raspyweather/githubHW/githubHW.cir

* C:\Users\Armin Beck\Documents\hw\githubHW.cir

* EESchema Netlist Version 1.1 (Spice format) creation date: 22.12.2017 06:53:42

* To exclude a component from the Spice Netlist add [Spice_Netlist_Enabled] user FIELD set to: N
* To reorder the component spice node sequence add [Spice_Node_Sequence] user FIELD and define sequence: 2,1,0

* Sheet Name: /
D65  Net-_D100-Pad1_ Net-_D50-Pad2_ LED		
D64  Net-_D106-Pad1_ Net-_D50-Pad2_ LED		
D66  Net-_D101-Pad1_ Net-_D50-Pad2_ LED		
D67  Net-_D102-Pad1_ Net-_D50-Pad2_ LED		
D68  Net-_D103-Pad1_ Net-_D50-Pad2_ LED		
D69  Net-_D104-Pad1_ Net-_D50-Pad2_ LED		
D70  Net-_D105-Pad1_ Net-_D50-Pad2_ LED		
D72  Net-_D100-Pad1_ Net-_D57-Pad2_ LED		
D71  Net-_D106-Pad1_ Net-_D57-Pad2_ LED		
D73  Net-_D101-Pad1_ Net-_D57-Pad2_ LED		
D74  Net-_D102-Pad1_ Net-_D57-Pad2_ LED		
D75  Net-_D103-Pad1_ Net-_D57-Pad2_ LED		
D76  Net-_D104-Pad1_ Net-_D57-Pad2_ LED		
D77  Net-_D105-Pad1_ Net-_D57-Pad2_ LED		
D79  Net-_D100-Pad1_ Net-_D78-Pad2_ LED		
D78  Net-_D106-Pad1_ Net-_D78-Pad2_ LED		
D80  Net-_D101-Pad1_ Net-_D78-Pad2_ LED		
D81  Net-_D102-Pad1_ Net-_D78-Pad2_ LED		
D82  Net-_D103-Pad1_ Net-_D78-Pad2_ LED		
D83  Net-_D104-Pad1_ Net-_D78-Pad2_ LED		
D84  Net-_D105-Pad1_ Net-_D78-Pad2_ LED		
D86  Net-_D100-Pad1_ Net-_D85-Pad2_ LED		
D85  Net-_D106-Pad1_ Net-_D85-Pad2_ LED		
D87  Net-_D101-Pad1_ Net-_D85-Pad2_ LED		
D88  Net-_D102-Pad1_ Net-_D85-Pad2_ LED		
D89  Net-_D103-Pad1_ Net-_D85-Pad2_ LED		
D90  Net-_D104-Pad1_ Net-_D85-Pad2_ LED		
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
D63  Net-_D14-Pad1_ Net-_D57-Pad2_ LED		
J2  Net-_D14-Pad1_ Net-_D13-Pad1_ Net-_D12-Pad1_ Net-_D11-Pad1_ Net-_D10-Pad1_ Net-_D16-Pad1_ Net-_D1-Pad1_ Conn_01x07		
J4  Net-_D14-Pad1_ Net-_D13-Pad1_ Net-_D12-Pad1_ Net-_D11-Pad1_ Net-_D10-Pad1_ Net-_D16-Pad1_ Net-_D1-Pad1_ Conn_01x07		
J3  Net-_D106-Pad1_ Net-_D100-Pad1_ Net-_D101-Pad1_ Net-_D102-Pad1_ Net-_D103-Pad1_ Net-_D104-Pad1_ Net-_D105-Pad1_ Conn_01x07		
J5  Net-_D106-Pad1_ Net-_D100-Pad1_ Net-_D101-Pad1_ Net-_D102-Pad1_ Net-_D103-Pad1_ Net-_D104-Pad1_ Net-_D105-Pad1_ Conn_01x07		
U3  Net-_D10-Pad2_ Net-_D15-Pad2_ Net-_D22-Pad2_ Net-_D29-Pad2_ Net-_D36-Pad2_ Net-_D43-Pad2_ Net-_D50-Pad2_ Net-_D57-Pad2_ Net-_D78-Pad2_ Net-_D85-Pad2_ Net-_D92-Pad2_ Net-_D100-Pad2_ Net-_D106-Pad2_ Net-_D113-Pad2_ Net-_D120-Pad2_ ? Net-_J6-Pad2_ /GSLCK +5V Net-_R1-Pad1_ +5V GND GND /LATCH /M_CLK Net-_J1-Pad2_ GND Net-_D1-Pad2_ TLC5940NT		
R1  Net-_R1-Pad1_ +5V R330		
J1  /M_CLK Net-_J1-Pad2_ +5V GND Conn_01x04		
J6  /M_CLK Net-_J6-Pad2_ +5V GND Conn_01x04		
U1  +5V GND /M_CLK /LATCH Net-_J1-Pad2_ /GSLCK ? ? ? Net-_RV1-Pad3_ Net-_SW4-Pad1_ Net-_SW3-Pad1_ Net-_SW2-Pad1_ Net-_SW1-Pad1_ Net-_U1-Pad15_ ? WeMos_mini		
SW1  Net-_SW1-Pad1_ +5V SW_Push		
SW2  Net-_SW2-Pad1_ +5V SW_Push		
SW3  Net-_SW3-Pad1_ +5V SW_Push		
SW4  Net-_SW4-Pad1_ +5V SW_Push		
RV1  ? +5V Net-_RV1-Pad3_ POT		
U2  ? +5V Net-_U1-Pad15_ Net-_D106-Pad1_ Net-_D100-Pad1_ Net-_D101-Pad1_ Net-_D102-Pad1_ +5V GND GND GND /LATCH /M_CLK Net-_D103-Pad1_ Net-_D104-Pad1_ Net-_D105-Pad1_ ? Net-_U2-Pad18_ GND ? TPIC6B595N		
U4  ? +5V Net-_U2-Pad18_ Net-_D105-Pad1_ Net-_D104-Pad1_ Net-_D103-Pad1_ Net-_D102-Pad1_ +5V GND GND GND /LATCH /M_CLK Net-_D101-Pad1_ Net-_D100-Pad1_ Net-_D106-Pad1_ ? ? GND ? TPIC6B595N		

.end
